OliverCuiriz/ComponentTester/PCB y esquematico - KiCad/PCB_Main.kicad_sch

## KiCad design PCB y esquematico - KiCad/PCB_Main.kicad_sch (2026-01-12)

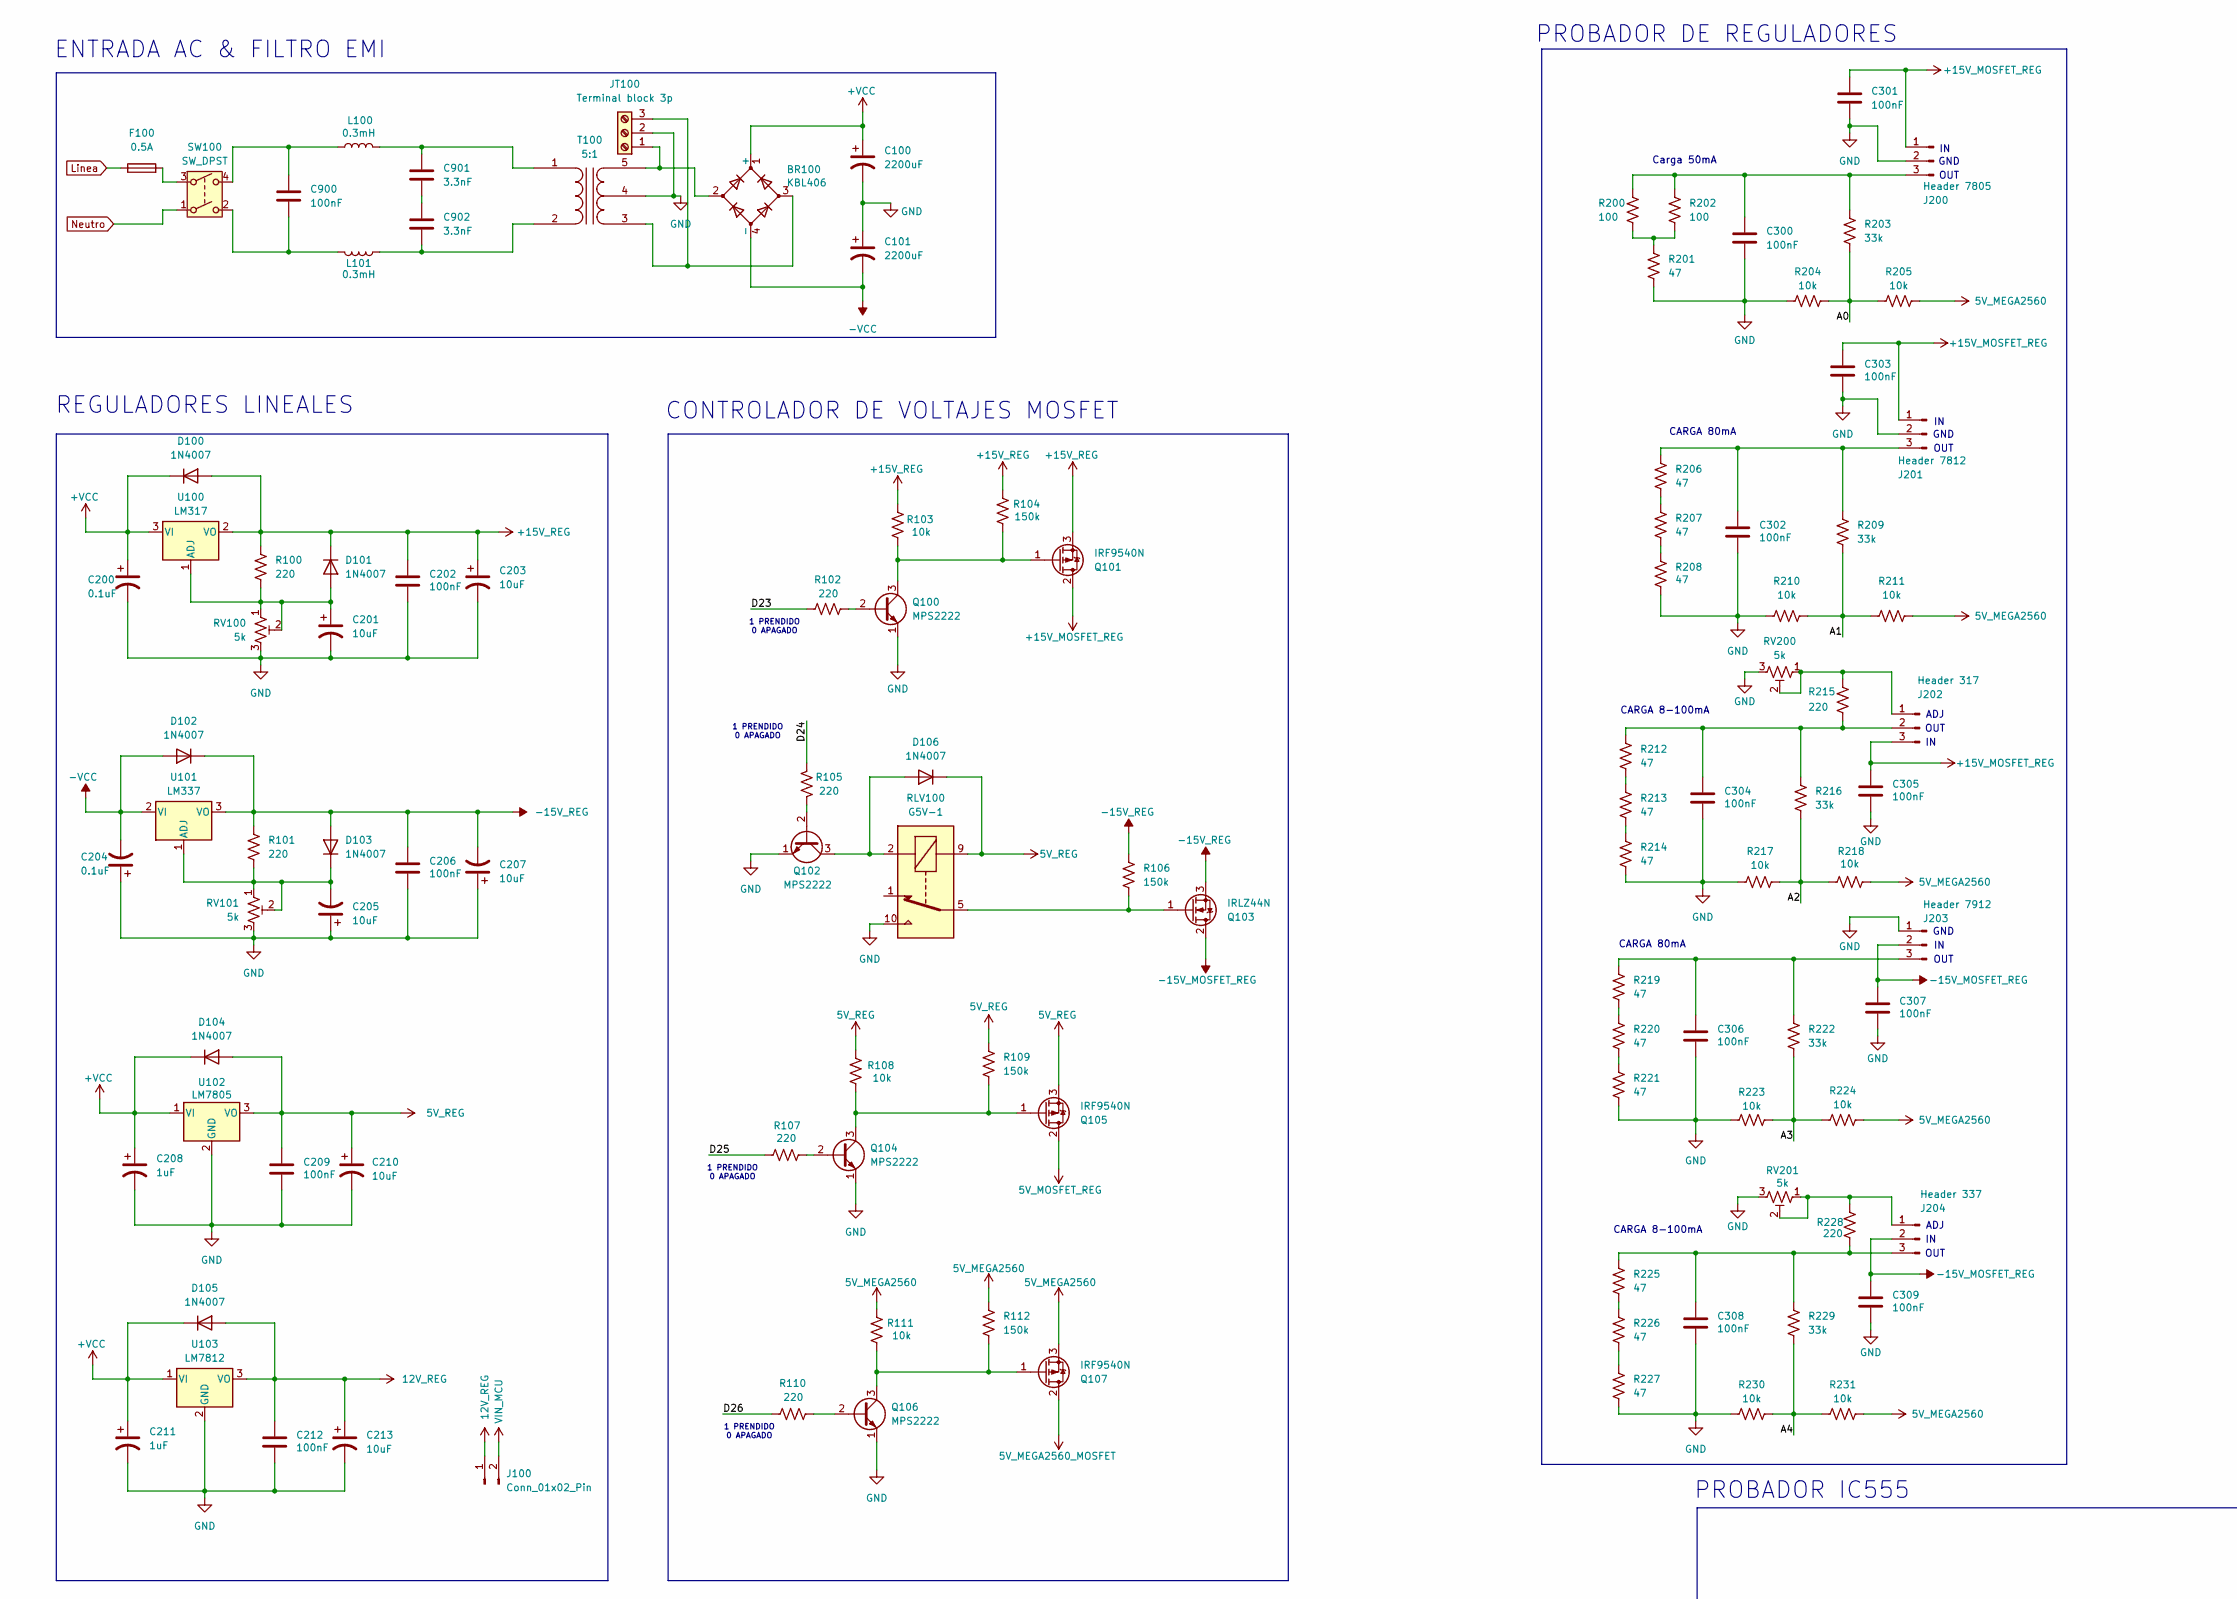
[picture p5: schematic PCB_Main.kicad_sch, part in row 1, column 1]

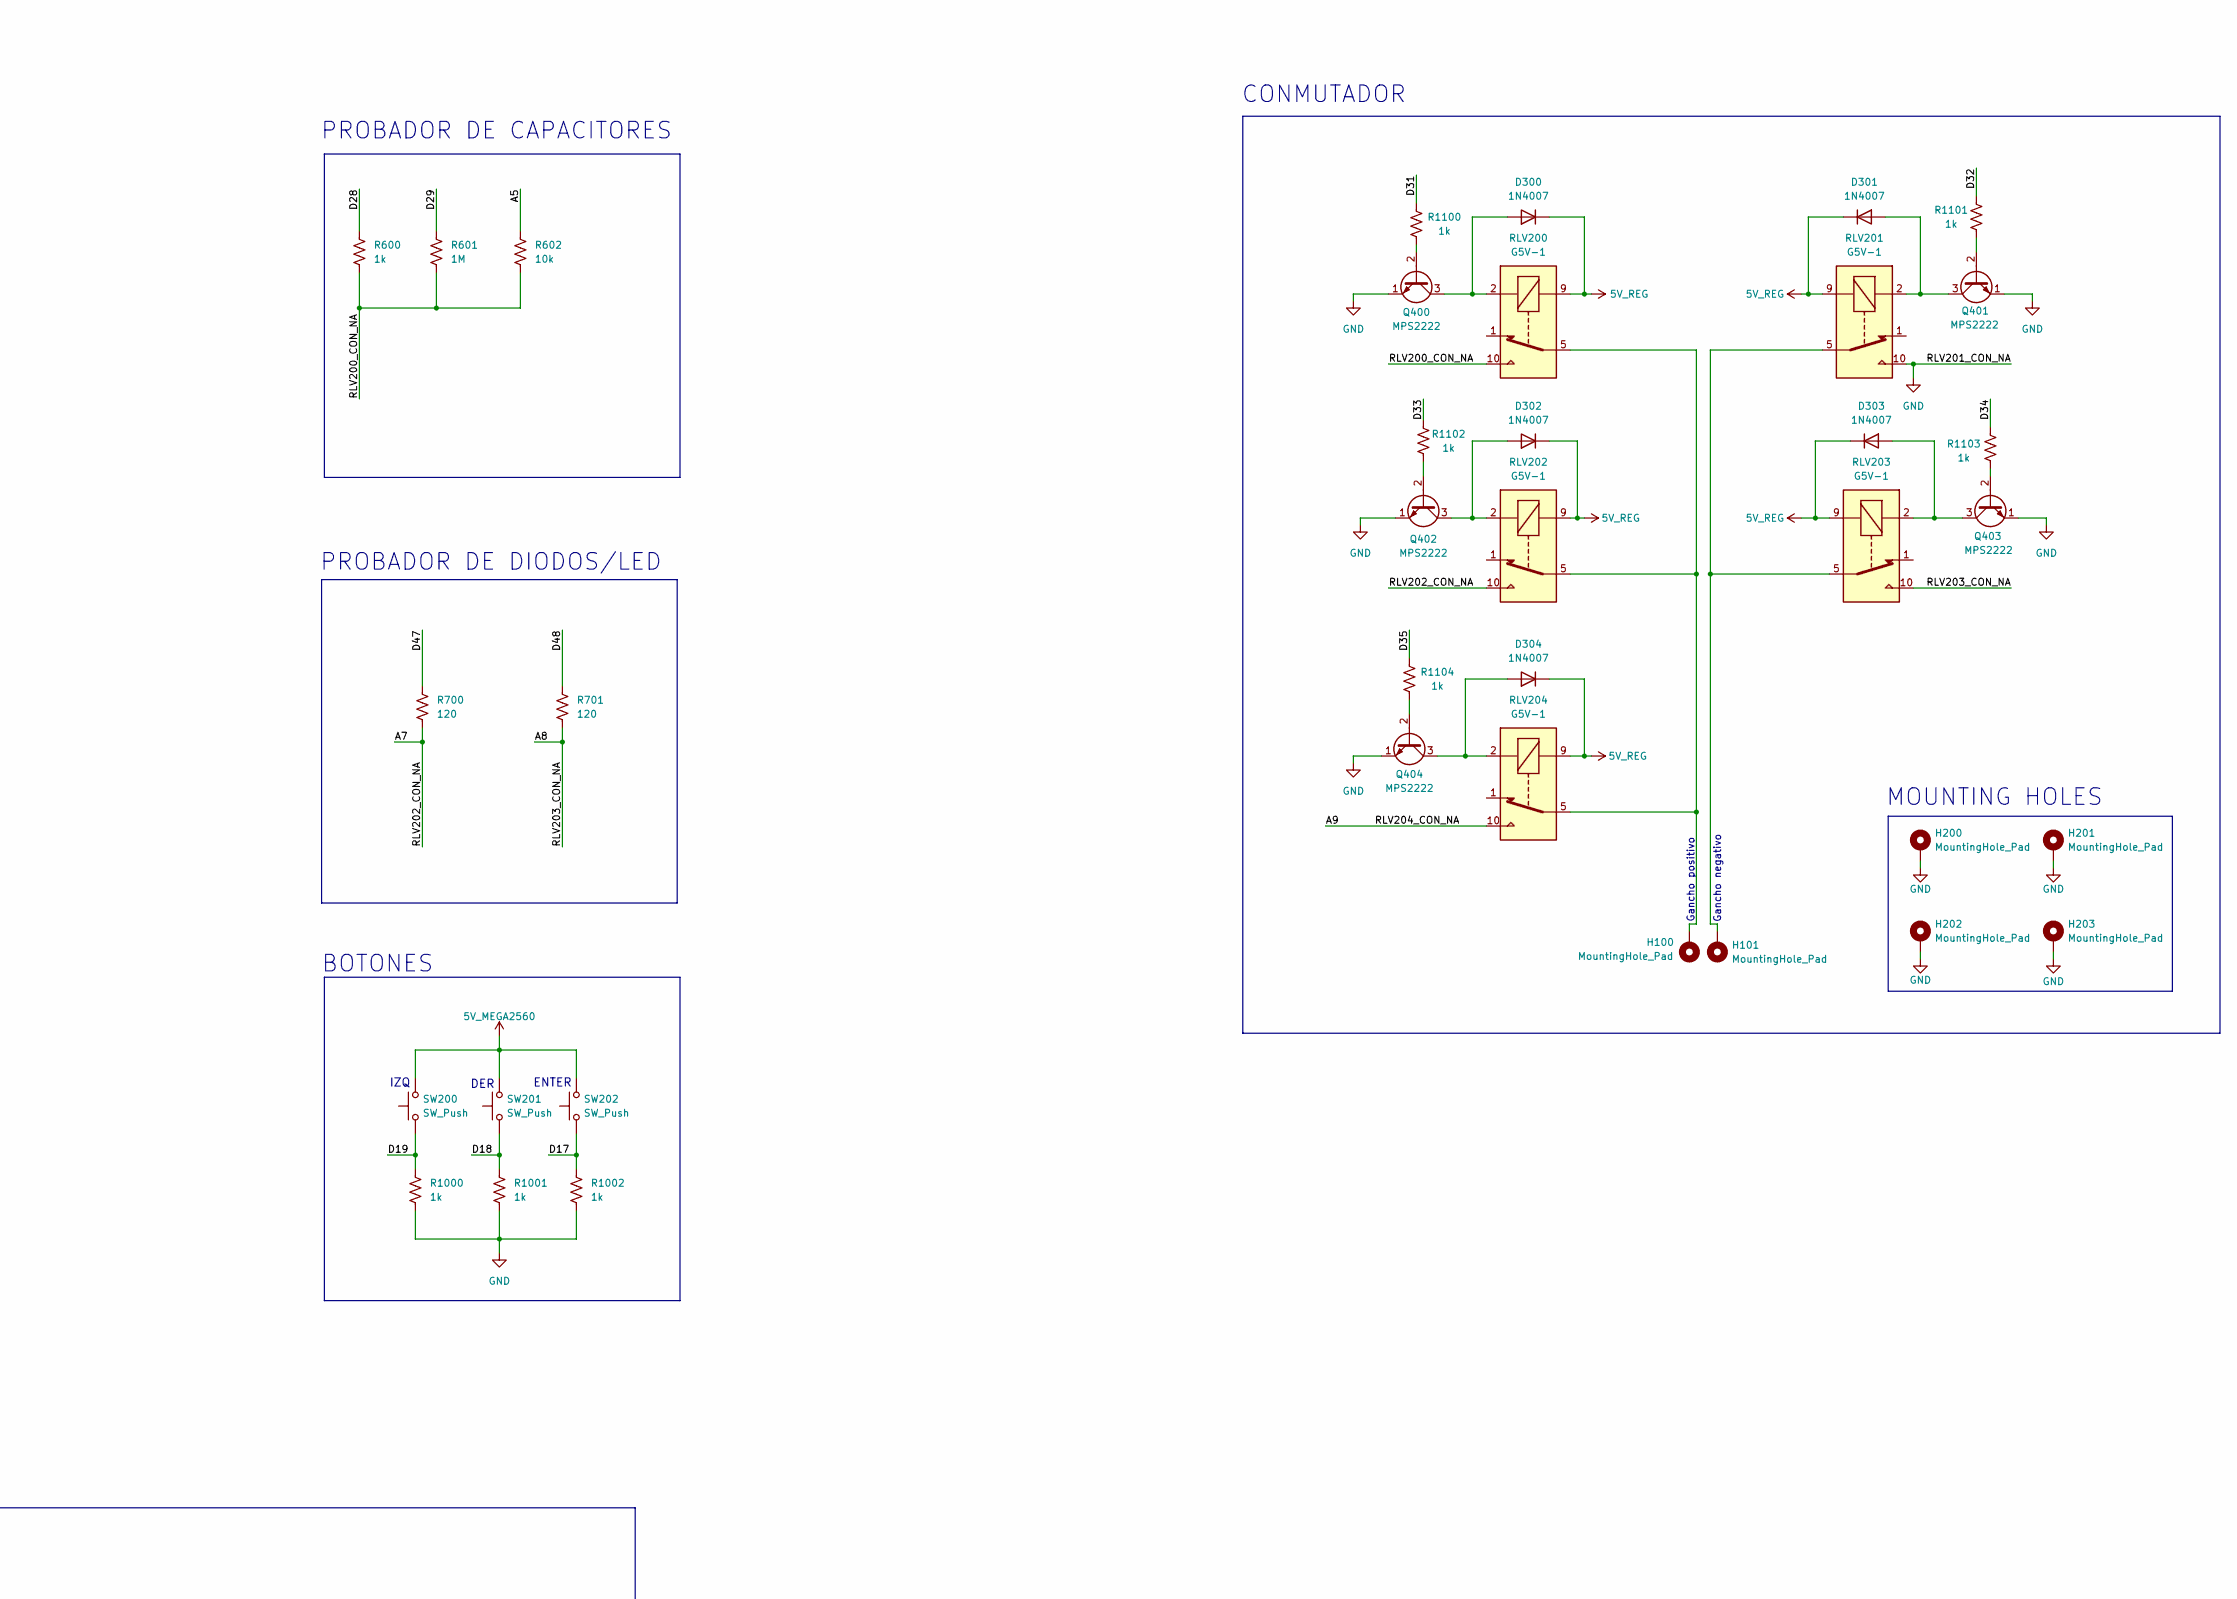
[picture p6: schematic PCB_Main.kicad_sch, part in row 1, column 2]

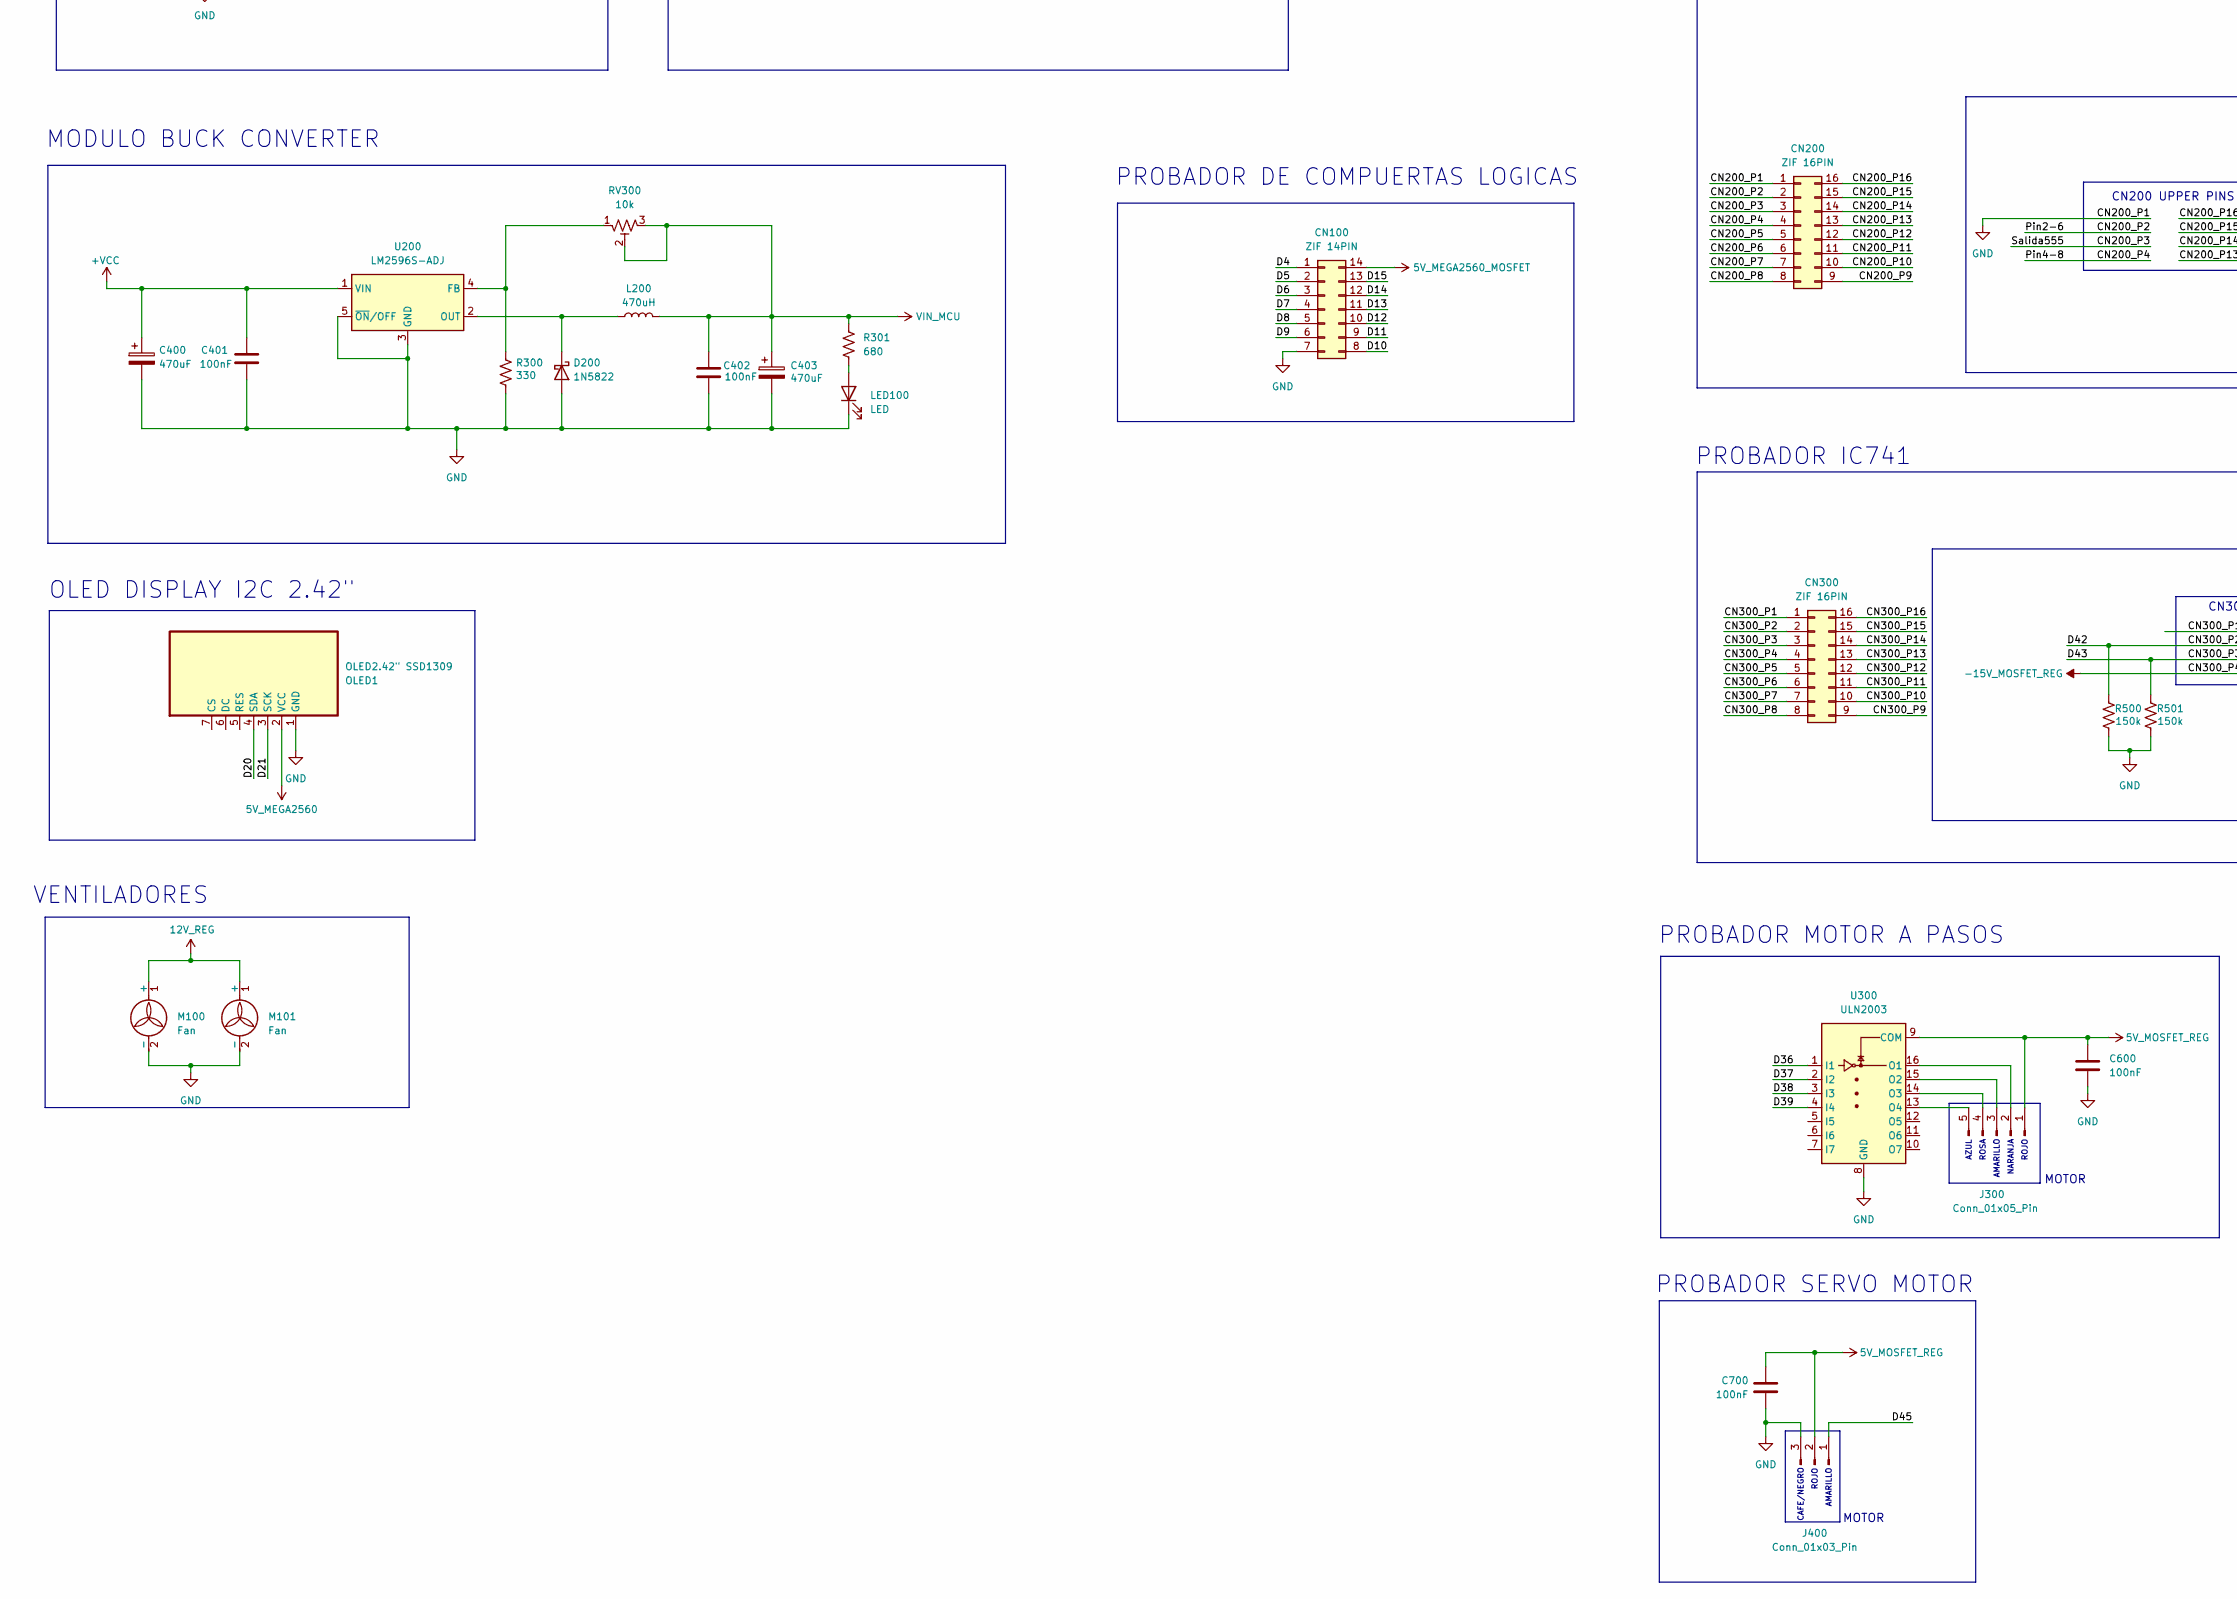
[picture p7: schematic PCB_Main.kicad_sch, part in row 2, column 1]

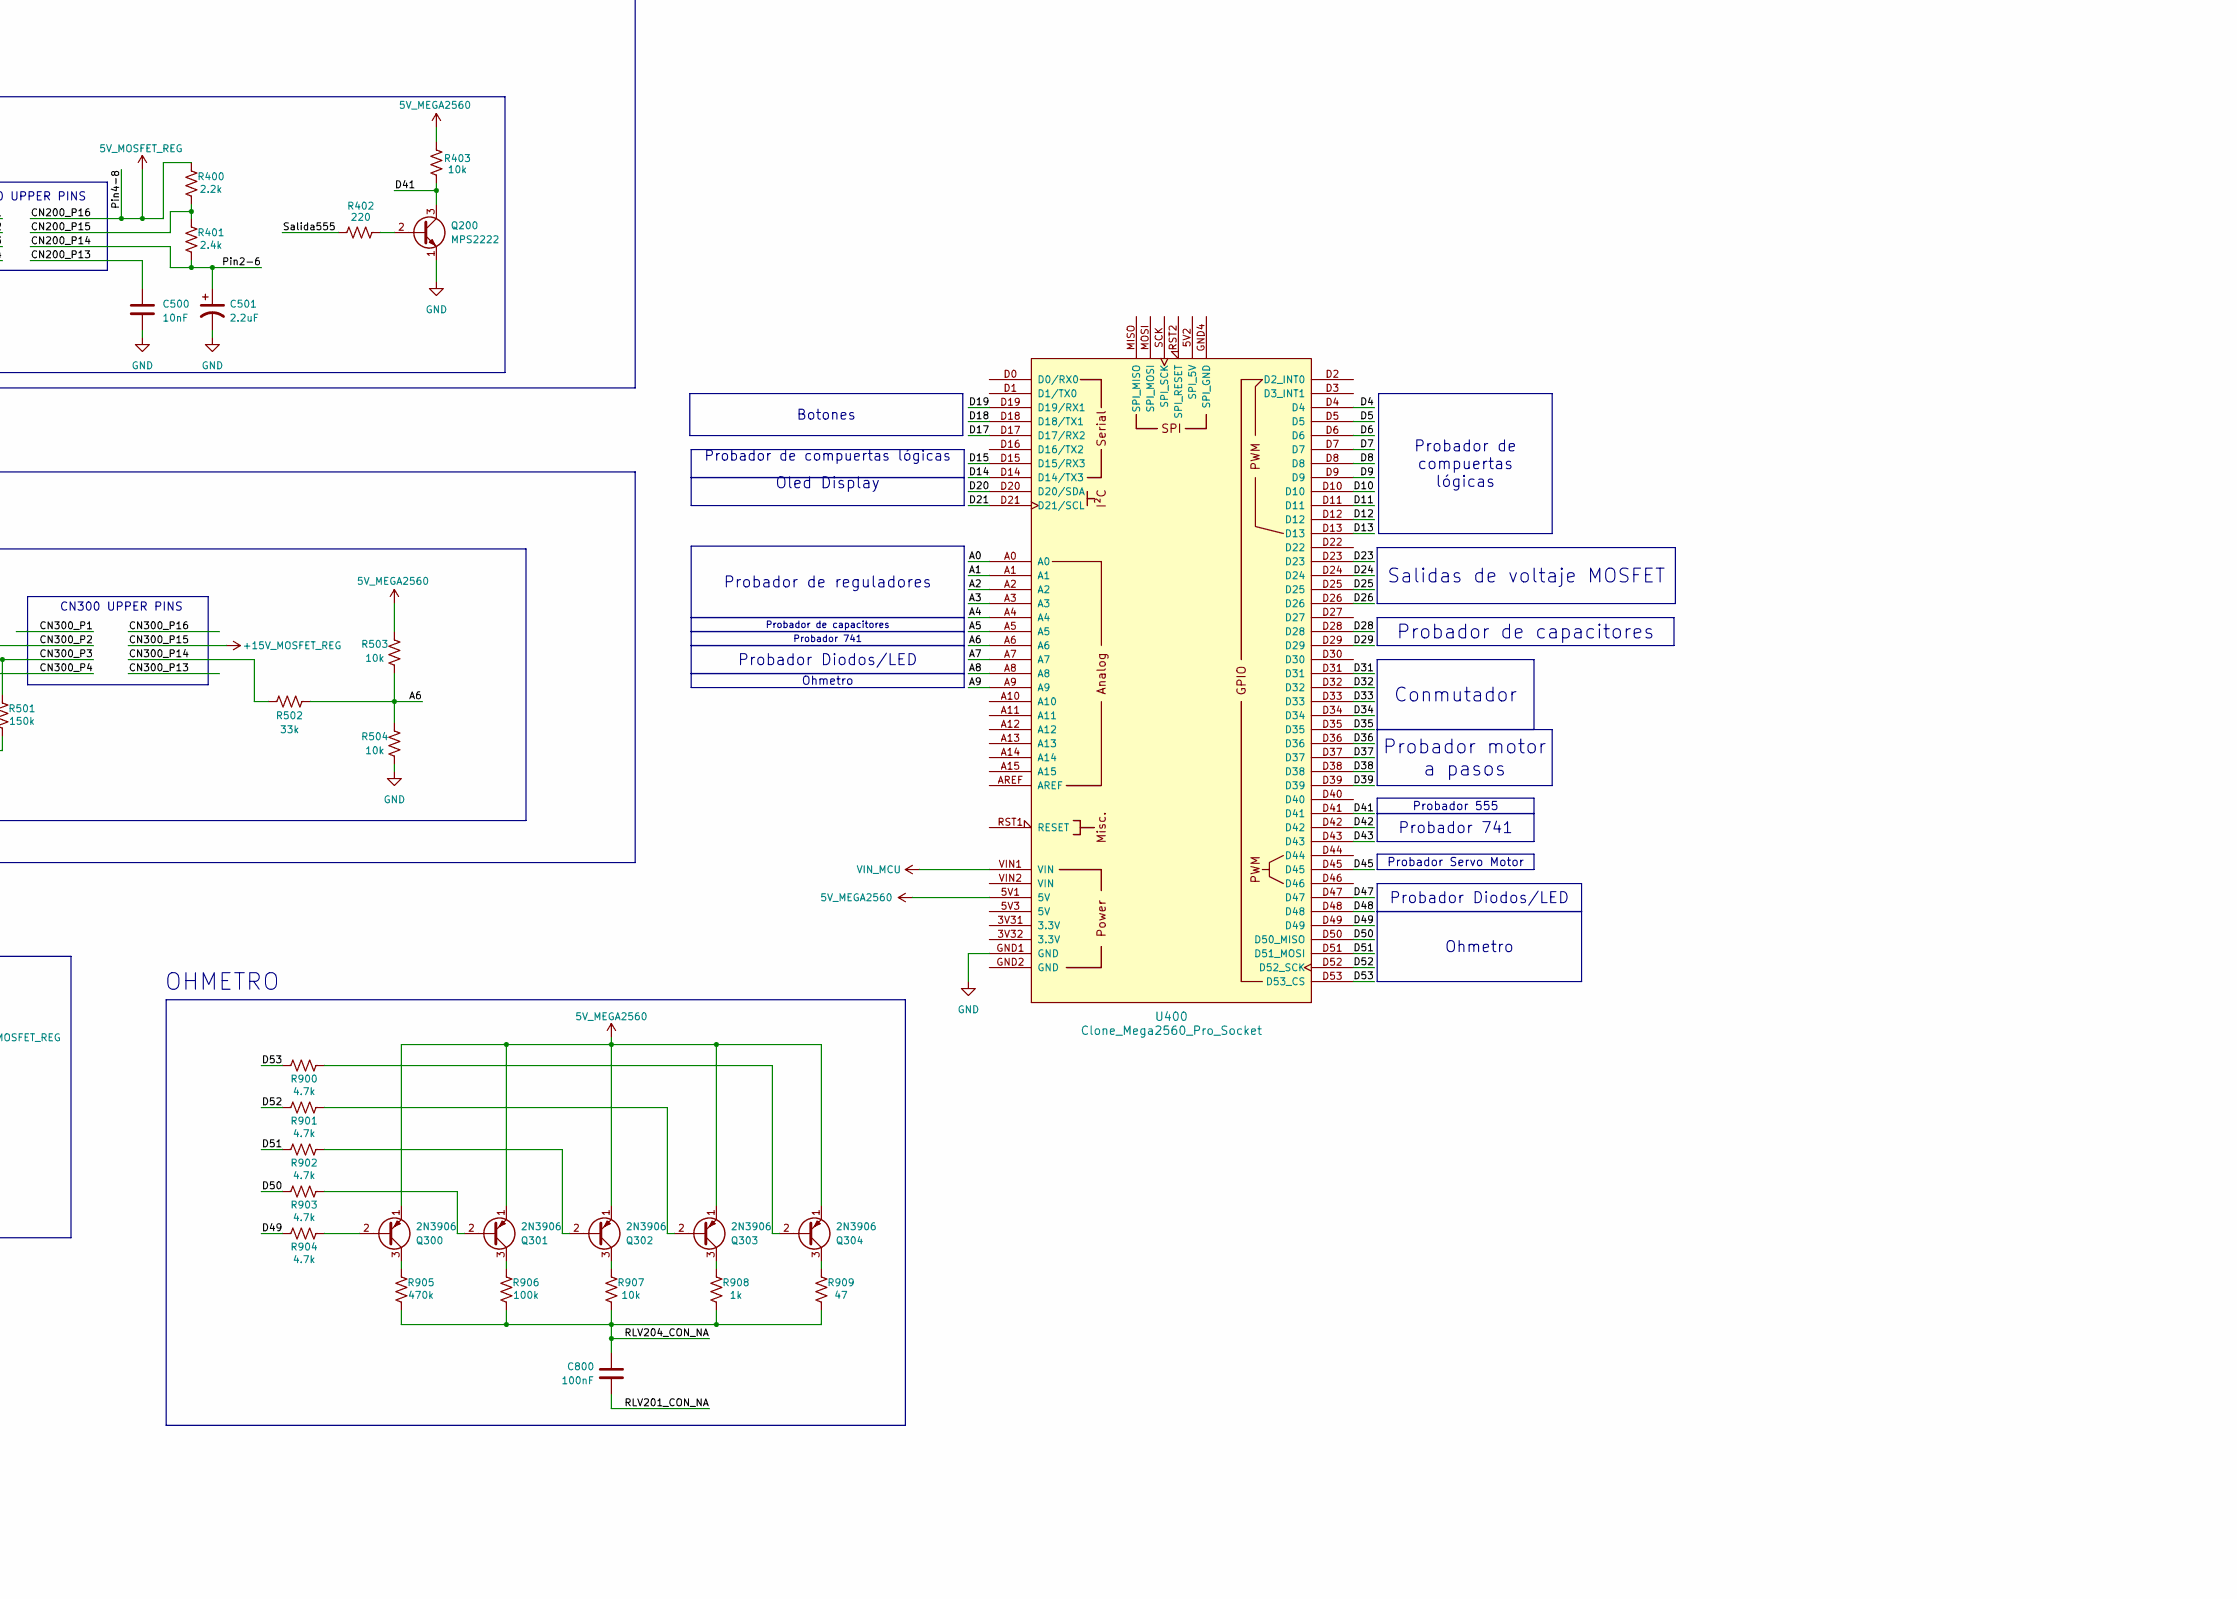
[picture p8: schematic PCB_Main.kicad_sch, part in row 2, column 2]

Parts:
BR100: KBL406; Diode_Bridge_Vishay_KBL
C100, C101: 2200uF; CP_Radial_D16.0mm_P7.50mm
C200, C204: 0.1uF; CP_Radial_D4.0mm_P2.00mm
C201, C203, C205, C207, C210, C213: 10uF; CP_Radial_D5.0mm_P2.50mm
C202, C206, C209, C212, C300, C301, C302, C303, C304, C305, C306, C307, C308, C309, C401, C402, C600, C700: 100nF; C_0805_2012Metric; LCSC Part # C28233
C208, C211: 1uF; CP_Radial_D5.0mm_P2.50mm
C400, C403: 470uF; CP_Radial_D8.0mm_P3.80mm
C500: 10nF; C_0805_2012Metric; LCSC Part # C1710
C501: 2.2uF; CP_Radial_D4.0mm_P2.00mm
C800: 100nF; C_Disc_D5.0mm_W2.5mm_P5.00mm
C900: 100nF
C901, C902: 3.3nF
CN100: ZIF 14PIN; DIP_Socket-14_W4.3_W5.08_W7.62_W10.16_W10.9_3M_214-3339-00-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
CN200, CN300: ZIF 16PIN; DIP_Socket-16_W4.3_W5.08_W7.62_W10.16_W10.9_3M_216-3340-00-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
D100, D101, D102, D103, D104, D105: 1N4007; D_DO-41_SOD81_P10.16mm_Horizontal
D106, D300, D301, D302, D303, D304: 1N4007; D_DO-41_SOD81_P2.54mm_Vertical_KathodeUp
D200: 1N5822; D_DO-201AD_P15.24mm_Horizontal
F100: 0.5A
H100, H101: MountingHole_Pad; MountingHole_5mm_Pad_TopBottom
H200, H201, H202, H203: MountingHole_Pad; MountingHole_4.3mm_M4_ISO14580_Pad_TopBottom
J100: Conn_01x02_Pin; PinHeader_1x02_P2.54mm_Vertical
J200: Header 7805; PinSocket_1x03_P2.54mm_Vertical
J201: Header 7812; PinSocket_1x03_P2.54mm_Vertical
J202: Header 317; PinSocket_1x03_P2.54mm_Vertical
J203: Header 7912; PinSocket_1x03_P2.54mm_Vertical
J204: Header 337; PinSocket_1x03_P2.54mm_Vertical
J300: Conn_01x05_Pin; JST_XH_B5B-XH-A_1x05_P2.50mm_Vertical
J400: Conn_01x03_Pin; PinHeader_1x03_P2.54mm_Vertical
JT100: Terminal block 3p; TerminalBlock_Phoenix_MKDS-1,5-3-5.08_1x03_P5.08mm_Horizont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
L100, L101: 0.3mH
L200: 470uH; L_Coilcraft_MSS1210H-XXX
LED100: LED; LED_D5.0mm
M100, M101: Fan; JST_XH_B2B-XH-A_1x02_P2.50mm_Vertical
OLED1: OLED2.42" SSD1309; OLED_SSD1309
Q100, Q102, Q104, Q106, Q200, Q400, Q401, Q402, Q403, Q404: MPS2222; TO-92_Inline
Q101, Q105, Q107: IRF9540N; TO-220-3_Vertical
Q103: IRLZ44N; TO-220-3_Vertical
Q300, Q301, Q302, Q303, Q304: 2N3906; TO-92_Inline
R100, R101, R102, R105, R107, R110, R215, R228, R402: 220; R_0805_2012Metric; LCSC Part # C17557
R103, R108, R111, R204, R205, R210, R211, R217, R218, R223, R224, R230, R231, R403, R503, R504: 10k; R_0805_2012Metric; LCSC Part # C17414
R104, R106, R109, R112, R500, R501: 150k; R_0805_2012Metric; LCSC Part # C17470
R200, R202: 100; R_Axial_DIN0309_L9.0mm_D3.2mm_P2.54mm_Vertical
R201, R206, R207, R208, R212, R213, R214, R219, R220, R221, R225, R226, R227: 47; R_Axial_DIN0309_L9.0mm_D3.2mm_P2.54mm_Vertical
R203, R209, R216, R222, R229, R502: 33k; R_0805_2012Metric; LCSC Part # C17633
R300: 330; R_0805_2012Metric; LCSC Part # C17630
R301: 680; R_0805_2012Metric; LCSC Part # C17798
R400: 2.2k; R_0805_2012Metric; LCSC Part # C17520
R401: 2.4k; R_0805_2012Metric; LCSC Part # C17526
R600, R908: 1k; R_Axial_DIN0207_L6.3mm_D2.5mm_P7.62mm_Horizontal
R601: 1M; R_Axial_DIN0207_L6.3mm_D2.5mm_P7.62mm_Horizontal
R602, R907: 10k; R_Axial_DIN0207_L6.3mm_D2.5mm_P7.62mm_Horizontal
R700, R701: 120; R_Axial_DIN0207_L6.3mm_D2.5mm_P7.62mm_Horizontal
R900, R901, R902, R903, R904: 4.7k; R_0805_2012Metric; LCSC Part # C17673
R905: 470k; R_Axial_DIN0207_L6.3mm_D2.5mm_P7.62mm_Horizontal
R906: 100k; R_Axial_DIN0207_L6.3mm_D2.5mm_P7.62mm_Horizontal
R909: 47; R_Axial_DIN0207_L6.3mm_D2.5mm_P7.62mm_Horizontal
R1000, R1001, R1002, R1100, R1101, R1102, R1103, R1104: 1k; R_0805_2012Metric; LCSC Part # C17513
RLV100, RLV200, RLV201, RLV202, RLV203, RLV204: G5V-1; Relay_SPDT_Omron_G5V-1
RV100, RV101: 5k; Potentiometer_Runtron_RM-065_Vertical
RV200, RV201: 5k; Potentiometer_Bourns_PTV09A-1_Single_Vertical
RV300: 10k; Potentiometer_Runtron_RM-065_Vertical
SW100: SW_DPST
SW200, SW201: SW_Push; SW_Cherry_MX_1.00u_Plate
SW202: SW_Push; SW_Cherry_MX_2.00u_Plate
T100: 5:1
U100: LM317; TO-220-3_Vertical
U101: LM337; TO-220-3_Vertical
U102: LM7805; TO-220-3_Vertical
U103: LM7812; TO-220-3_Vertical
U200: LM2596S-ADJ; TO-263-5_TabPin3
U300: ULN2003; DIP-16_W7.62mm
U400: Clone_Mega2560_Pro_Socket; Clone_Mega2560_Pro_Socket_EDITADO

Connections:
5V_MEGA2560: OLED1.2 (VCC), Q107.3 (S), Q300.1 (E), Q301.1 (E), Q302.1 (E), Q303.1 (E), Q304.1 (E), R111.2, R112.1, R205.1, R211.1, R218.1, R224.1, R231.1, R403.1, R503.1, SW200.2, SW201.2, SW202.2, U400.5V1 (5V)
5V_MEGA2560_MOSFET: CN100.14, Q107.2 (D)
5V_MOSFET_REG: C600.1, C700.2, CN200.4, CN200.16, J300.1, J400.2, Q105.2 (D), R400.1, U300.9 (COM)
5V_REG: C209.1, C210.1, D104.2 (A), D106.1 (K), D300.1 (K), D301.1 (K), D302.1 (K), D303.1 (K), D304.1 (K), Q105.3 (S), R108.2, R109.1, RLV100.9, RLV200.9, RLV201.9, RLV202.9, RLV203.9, RLV204.9, U102.3 (VO)
12V_REG: C212.1, C213.1, D105.2 (A), J100.1, M100.1 (+), M101.1 (+), U103.3 (VO)
+15V_MOSFET_REG: C301.1, C303.1, C305.1, CN300.15, J200.1, J201.1, J202.3, Q101.2 (D)
+15V_REG: C202.1, C203.1, D100.2 (A), D101.1 (K), Q101.3 (S), R100.1, R103.2, R104.1, U100.2 (VO)
+VCC: BR100.1 (+), C100.1, C200.1, C208.1, C211.1, C400.1, C401.1, D100.1 (K), D104.1 (K), D105.1 (K), U100.3 (VI), U102.1 (VI), U103.1 (VI), U200.1 (VIN)
-15V_MOSFET_REG: C307.1, C309.1, CN300.4, J203.2, J204.2, Q103.2 (D)
-15V_REG: C206.1, C207.2, D102.1 (K), D103.2 (A), Q103.3 (S), R101.1, R106.1, U101.3 (VO)
-VCC: BR100.4 (-), C101.2, C204.2, D102.2 (A), U101.2 (VI)
A0: R203.2, R204.2, R205.2, U400.A0
A1: R209.2, R210.2, R211.2, U400.A1
A2: R216.2, R217.2, R218.2, U400.A2
A3: R222.2, R223.2, R224.2, U400.A3
A4: R229.2, R230.2, R231.2, U400.A4
A5: R602.1, U400.A5
A6: R502.2, R503.2, R504.2, U400.A6
A7: R700.2, RLV202.10, U400.A7
A8: R701.2, RLV203.10, U400.A8
A9: C800.2, R905.2, R906.2, R907.2, R908.2, R909.2, RLV204.10, U400.A9
CN200_P3: CN200.3, R402.1
CN200_P5: CN200.5
CN200_P6: CN200.6
CN200_P7: CN200.7
CN200_P8: CN200.8
CN200_P9: CN200.9
CN200_P10: CN200.10
CN200_P11: CN200.11
CN200_P12: CN200.12
CN200_P13: C500.1, CN200.13
CN200_P14: C501.1, CN200.2, CN200.14, R401.2
CN200_P15: CN200.15, R400.2, R401.1
CN300_P1: CN300.1
CN300_P2: CN300.2, R500.1, U400.D42
CN300_P3: CN300.3, R501.1, U400.D43
CN300_P5: CN300.5
CN300_P6: CN300.6
CN300_P7: CN300.7
CN300_P8: CN300.8
CN300_P9: CN300.9
CN300_P10: CN300.10
CN300_P11: CN300.11
CN300_P12: CN300.12
CN300_P13: CN300.13
CN300_P14: CN300.14, R502.1
CN300_P16: CN300.16
D4: CN100.1, U400.D4
D5: CN100.2, U400.D5
D6: CN100.3, U400.D6
D7: CN100.4, U400.D7
D8: CN100.5, U400.D8
D9: CN100.6, U400.D9
D10: CN100.8, U400.D10
D11: CN100.9, U400.D11
D12: CN100.10, U400.D12
D13: CN100.11, U400.D13
D14: CN100.12, U400.D14 (D14/TX3)
D15: CN100.13, U400.D15 (D15/RX3)
D17: R1002.1, SW202.1, U400.D17 (D17/RX2)
D18: R1001.1, SW201.1, U400.D18 (D18/TX1)
D19: R1000.1, SW200.1, U400.D19 (D19/RX1)
D20: OLED1.4 (SDA), U400.D20 (D20/SDA)
D21: OLED1.3 (SCK), U400.D21 (D21/SCL)
D23: R102.1, U400.D23
D24: R105.1, U400.D24
D25: R107.1, U400.D25
D26: R110.1, U400.D26
D28: R600.1, U400.D28
D29: R601.1, U400.D29
D31: R1100.1, U400.D31
D32: R1101.1, U400.D32
D33: R1102.1, U400.D33
D34: R1103.1, U400.D34
D35: R1104.1, U400.D35
D36: U300.1 (I1), U400.D36
D37: U300.2 (I2), U400.D37
D38: U300.3 (I3), U400.D38
D39: U300.4 (I4), U400.D39
D41: Q200.3 (C), R403.2, U400.D41
D45: J400.1, U400.D45
D47: R700.1, U400.D47
D48: R701.1, U400.D48
D49: R904.2, U400.D49
D50: R903.2, U400.D50 (D50_MISO)
D51: R902.2, U400.D51 (D51_MOSI)
D52: R901.2, U400.D52 (D52_SCK)
D53: R900.2, U400.D53 (D53_CS)
GND: C100.2, C101.1, C200.2, C201.2, C202.2, C203.2, C204.1, C205.1, C206.2, C207.1, C208.2, C209.2, C210.2, C211.2, C212.2, C213.2, C300.2, C301.2, C302.2, C303.2, C304.2, C305.2, C306.2, C307.2, C308.2, C309.2, C400.2, C401.2, C402.2, C403.2, C500.2, C501.2, C600.2, C700.1, C800.1, CN100.7, CN200.1, D200.2 (A), H200.1, H201.1, H202.1, H203.1, J200.2, J201.2, J203.1, J400.3, JT100.2, LED100.1 (K), M100.2 (-), M101.2 (-), OLED1.1 (GND), Q100.1 (E), Q102.1 (E), Q104.1 (E), Q106.1 (E), Q200.1 (E), Q400.1 (E), Q401.1 (E), Q402.1 (E), Q403.1 (E), Q404.1 (E), R201.2, R204.1, R208.2, R210.1, R214.2, R217.1, R221.2, R223.1, R227.2, R230.1, R300.2, R500.2, R501.2, R504.1, R1000.2, R1001.2, R1002.2, RLV100.10, RLV201.10, RV100.3, RV101.3, RV200.3, RV201.3, T100.4 (SC), U102.2 (GND), U103.2 (GND), U200.3 (GND), U200.5 (~ON/OFF), U300.8 (GND), U400.GND1 (GND)
Linea: F100.1
unnamed: BR100.2, JT100.1, T100.5 (SB)
unnamed: BR100.3, JT100.3, T100.3 (SA)
unnamed: C201.1, D101.2 (A), R100.2, RV100.1, RV100.2, U100.1 (ADJ)
unnamed: C205.2, D103.1 (K), R101.2, RV101.1, RV101.2, U101.1 (ADJ)
unnamed: C300.1, J200.3, R200.1, R202.1, R203.1
unnamed: C302.1, J201.3, R206.1, R209.1
unnamed: C304.1, J202.2, R212.1, R215.2, R216.1
unnamed: C306.1, J203.3, R219.1, R222.1
unnamed: C308.1, J204.3, R225.1, R228.1, R229.1
unnamed: C900.1, L100.1, SW100.4
unnamed: C900.2, L101.2, SW100.2
unnamed: C901.1, L100.2, T100.1 (AA)
unnamed: C901.2, C902.1
unnamed: C902.2, L101.1, T100.2 (AB)
unnamed: D106.2 (A), Q102.3 (C), RLV100.2
unnamed: D200.1 (K), L200.1, U200.2 (OUT)
unnamed: D300.2 (A), Q400.3 (C), RLV200.2
unnamed: D301.2 (A), Q401.3 (C), RLV201.2
unnamed: D302.2 (A), Q402.3 (C), RLV202.2
unnamed: D303.2 (A), Q403.3 (C), RLV203.2
unnamed: D304.2 (A), Q404.3 (C), RLV204.2
unnamed: F100.2, SW100.3
unnamed: H100.1, RLV200.5, RLV200.6, RLV202.5, RLV202.6, RLV204.5, RLV204.6
unnamed: H101.1, RLV201.5, RLV201.6, RLV203.5, RLV203.6
unnamed: J202.1, R215.1, RV200.1, RV200.2
unnamed: J204.1, R228.2, RV201.1, RV201.2
unnamed: J300.2, U300.16 (O1)
unnamed: J300.3, U300.15 (O2)
unnamed: J300.4, U300.14 (O3)
unnamed: J300.5, U300.13 (O4)
unnamed: LED100.2 (A), R301.2
unnamed: Q100.2 (B), R102.2
unnamed: Q100.3 (C), Q101.1 (G), R103.1, R104.2
unnamed: Q102.2 (B), R105.2
unnamed: Q103.1 (G), R106.2, RLV100.5, RLV100.6
unnamed: Q104.2 (B), R107.2
unnamed: Q104.3 (C), Q105.1 (G), R108.1, R109.2
unnamed: Q106.2 (B), R110.2
unnamed: Q106.3 (C), Q107.1 (G), R111.1, R112.2
unnamed: Q200.2 (B), R402.2
unnamed: Q300.2 (B), R904.1
unnamed: Q300.3 (C), R905.1
unnamed: Q301.2 (B), R903.1
unnamed: Q301.3 (C), R906.1
unnamed: Q302.2 (B), R902.1
unnamed: Q302.3 (C), R907.1
unnamed: Q303.2 (B), R901.1
unnamed: Q303.3 (C), R908.1
unnamed: Q304.2 (B), R900.1
unnamed: Q304.3 (C), R909.1
unnamed: Q400.2 (B), R1100.2
unnamed: Q401.2 (B), R1101.2
unnamed: Q402.2 (B), R1102.2
unnamed: Q403.2 (B), R1103.2
unnamed: Q404.2 (B), R1104.2
unnamed: R200.2, R201.1, R202.2
unnamed: R206.2, R207.1
unnamed: R207.2, R208.1
unnamed: R212.2, R213.1
unnamed: R213.2, R214.1
unnamed: R219.2, R220.1
unnamed: R220.2, R221.1
unnamed: R225.2, R226.1
unnamed: R226.2, R227.1
unnamed: R300.1, RV300.1, U200.4 (FB)
Neutro: SW100.1
RLV200_CON_NA: R600.2, R601.2, R602.2, RLV200.10
VIN_MCU: C402.1, C403.1, J100.2, L200.2, R301.1, RV300.2, RV300.3, U400.VIN1 (VIN)

Notes on the sheet:
AZUL
IZQ
PROBADOR DE COMPUERTAS LOGICAS
ENTER
GND
DER
OUT
CARGA 8-100mA
ADJ
OLED DISPLAY I2C 2.42"
Gancho negativo
OHMETRO
ENTRADA AC & FILTRO EMI
PROBADOR DE DIODOS/LED
AMARILLO
CONMUTADOR
MOTOR
REGULADORES LINEALES
CARGA 80mA
PROBADOR SERVO MOTOR
ROSA
PROBADOR DE REGULADORES
PROBADOR IC555
VENTILADORES
Carga 50mA
Gancho positivo
CN200 UPPER PINS
ROJO
PROBADOR MOTOR A PASOS
BOTONES
1 PRENDIDO 0 APAGADO
PROBADOR IC741
PROBADOR DE CAPACITORES
CAFE/NEGRO
CN300 UPPER PINS
MODULO BUCK CONVERTER
NARANJA
MOUNTING HOLES
CONTROLADOR DE VOLTAJES MOSFET
Ohmetro
Probador de reguladores
Probador Diodos/LED
Probador motor a pasos
Probador de capacitores
Salidas de voltaje MOSFET
Probador 741
Botones
Probador Servo Motor
Probador de compuertas lógicas
Oled Display
Probador 555
Probador de compuertas lógicas
Conmutador
