OliverCuiriz/ComponentTester/Codigo del proyecto - Arduino IDE/iconos.h

// ' icono 74LS00', 16x16px
const unsigned char epd_bitmap__icono_74LS00 [] PROGMEM = {
	0x00, 0x00, 0x00, 0x1e, 0x80, 0x33, 0xe0, 0x60, 0x38, 0xc0, 0x0e, 0xe0, 0x03, 0xb8, 0x01, 0xae, 
	0x85, 0xab, 0xe3, 0x2a, 0xb5, 0x0a, 0xad, 0x02, 0xa9, 0x00, 0x28, 0x00, 0x08, 0x00, 0x00, 0x00
};
// ' icono 74LS02', 16x16px
const unsigned char epd_bitmap__icono_74LS02 [] PROGMEM = {
	0x00, 0x00, 0x00, 0x1e, 0x80, 0x33, 0xe0, 0x60, 0x38, 0xc0, 0x0e, 0xe0, 0x03, 0xb8, 0x01, 0xae, 
	0x85, 0xab, 0xe3, 0x2a, 0xb5, 0x0a, 0xad, 0x02, 0xa9, 0x00, 0x28, 0x00, 0x08, 0x00, 0x00, 0x00
};
// ' icono 74LS04', 16x16px
const unsigned char epd_bitmap__icono_74LS04 [] PROGMEM = {
	0x00, 0x00, 0x00, 0x1e, 0x80, 0x33, 0xe0, 0x60, 0x38, 0xc0, 0x0e, 0xe0, 0x03, 0xb8, 0x01, 0xae, 
	0x85, 0xab, 0xe3, 0x2a, 0xb5, 0x0a, 0xad, 0x02, 0xa9, 0x00, 0x28, 0x00, 0x08, 0x00, 0x00, 0x00
};
// ' icono 74LS08', 16x16px
const unsigned char epd_bitmap__icono_74LS08 [] PROGMEM = {
	0x00, 0x00, 0x00, 0x1e, 0x80, 0x33, 0xe0, 0x60, 0x38, 0xc0, 0x0e, 0xe0, 0x03, 0xb8, 0x01, 0xae, 
	0x85, 0xab, 0xe3, 0x2a, 0xb5, 0x0a, 0xad, 0x02, 0xa9, 0x00, 0x28, 0x00, 0x08, 0x00, 0x00, 0x00
};
// ' icono 74LS32', 16x16px
const unsigned char epd_bitmap__icono_74LS32 [] PROGMEM = {
	0x00, 0x00, 0x00, 0x1e, 0x80, 0x33, 0xe0, 0x60, 0x38, 0xc0, 0x0e, 0xe0, 0x03, 0xb8, 0x01, 0xae, 
	0x85, 0xab, 0xe3, 0x2a, 0xb5, 0x0a, 0xad, 0x02, 0xa9, 0x00, 0x28, 0x00, 0x08, 0x00, 0x00, 0x00
};
// ' icono 74LS86', 16x16px
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
	0x00, 0x00, 0x00, 0x00, 0x00, 0x80, 0x87, 0x87, 0x88, 0x80, 0x00, 0x00, 0x00, 0x00, 0x00, 0x00, 
	0x01, 0x00, 0x00, 0x00, 0x00, 0x00, 0x00, 0x00, 0x00, 0x00, 0x00, 0x00, 0x00, 0x00, 0x00, 0x80, 
	0xdb, 0xb6, 0x6d, 0xdb, 0xb6, 0x6d, 0xdb, 0xb6, 0x6d, 0xdb, 0xb6, 0x6d, 0xdb, 0xb6, 0x6d, 0xdb
};
